TheShadow507-gif/WRO2026_SENTINELS/schemes/Esquema_del_circuito.png

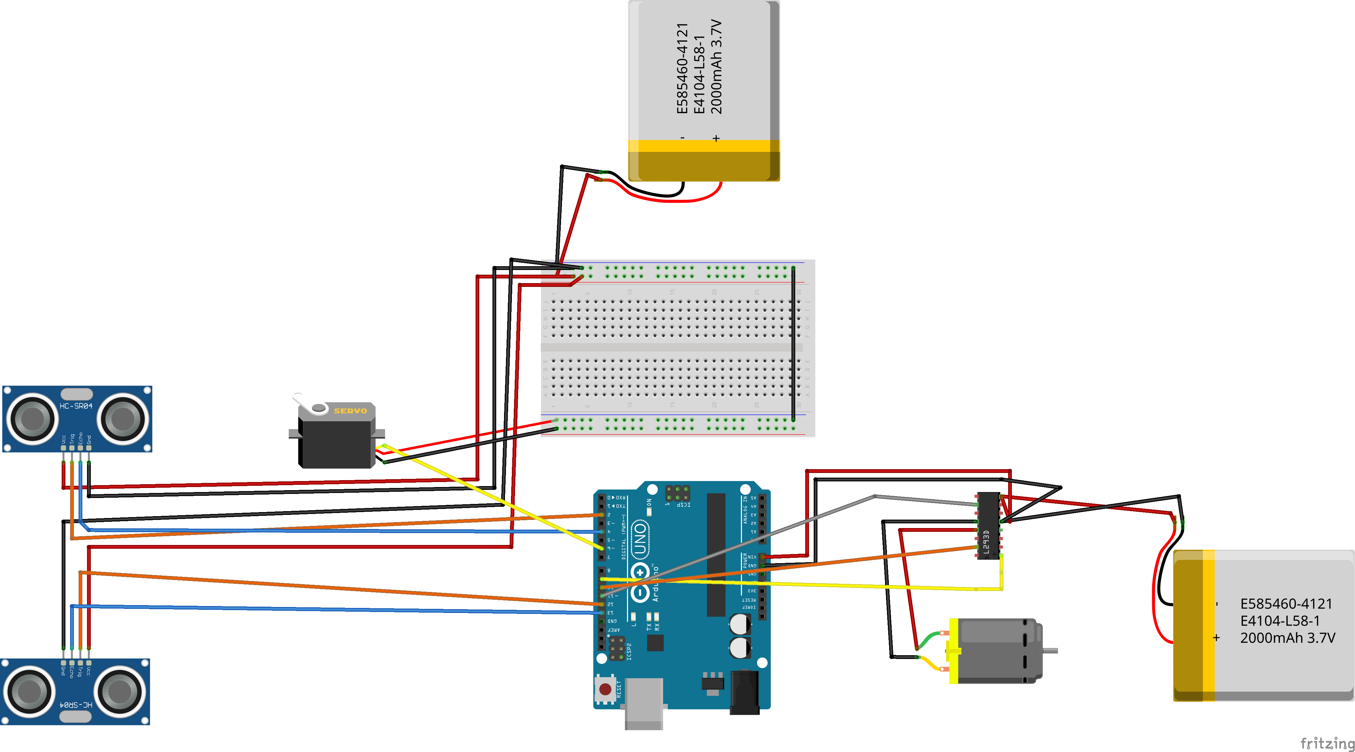
schemes/Esquema_del_circuito.png
